tonykoop/chalumeau/build/packet/validation.csv

test_id | variant | target | target_value | measured_value | tolerance | environment | pass_condition | blocking_unknowns | result | action
VAL-001 | all | A4 reference | 440.00 Hz |  | tuner reads 440 within calibration | record temp F, humidity percent | tuner/mic calibration logged before any pitch row | calibrated tuner or reference tone |  | Calibrate tuner/mic before instrument data.
VAL-005 | Soprano C | reed and mouthpiece setup | one reed_id and mouthpiece_id recorded in reed-mouthpiece-capture-template.csv |  | required before pitch claims | same setup ID must appear in prototype/tuning logs | selected setup has reed/mouthpiece identity, gap, onset pressure, response, and leak status | reed model/strength, mouthpiece model/facing, onset pressure, response |  | Do not compare pitch sessions until reed/mouthpiece IDs match.
VAL-008 | Soprano C | bore and trim capture | bore stations plus trim state recorded in bore-trim-capture-template.csv |  | required before final tone-hole tuning | measure before and after bell/foot trim | bore profile and trim history are tied to all-closed measured pitch with the same setup IDs | reed-seat datum, bore station values, measured root pitch |  | Resolve taper/ovalization or datum mismatch before drilling final holes.
VAL-010 | Soprano C | all holes closed | C4, 261.63 Hz |  | +/- 15 cents before final tuning; +/- 8 cents after | 68-72 F preferred | all-closed pitch is logged with reed_id, mouthpiece_id, bore_profile_id, response, and onset pressure | measured_hz, cents_error, response, onset pressure |  | Trim bell end shorter to sharpen; add temporary tape/extension if sharp.
VAL-020 | all | tone-hole sweep | each row in data/tone-hole-schedule.csv |  | +/- 12 cents after tuning | same reed_id, mouthpiece_id, bore_profile_id, and blowing pressure | H01-H07 final rows are within tolerance with response_rating_1_5 >= 3 | final hole diameters, measured_hz, cents_error, response |  | Open hole diameter to sharpen; use wax/tape collar to flatten during tests.
VAL-025 | Soprano C | response sweep | response_rating_1_5 >= 3 and onset_pressure_in_h2o recorded for all closed plus H01-H07 |  | no missing response rows in tuning-capture-template.csv | same reed/mouthpiece setup as tone-hole sweep | every accepted tuning row has onset pressure, response, leak check, and action if response is poor | onset pressure, leak result, response for every note |  | If a note speaks late or chirps, fix leak/reed setup before enlarging holes.
VAL-030 | keyed builds | pad leak test | no visible leak under leak light; suction holds 10 s |  | zero audible hiss at normal blowing pressure | before final tone-hole tuning | K01/K02 pitch rows are accepted only after a leak-light or suction pass | pad seating evidence, suction duration, keyed response |  | Reseat pad, regulate cork, or lap tone-hole rim.
VAL-040 | experimental register key | overblown twelfth check | note + 19 semitones if vent is clarinet-like |  | document response only; not a first-build pass/fail | same reed and embouchure as low-register test | register behavior is logged as research and does not promote first-build readiness | stable low-register response, measured vent response |  | Move/resize vent only after the core chalumeau speaks well.
