tonykoop/chalumeau/validation.csv

gate_id | area | current_status | evidence | pass_condition | blocking_unknowns | next_action | promotion_blocker
VAL-BB-001 | readiness | prototype-validation scaffold | Root packet plus existing build/packet artifacts | All measurement gates below have recorded evidence before L3/build-ready language | measured prototype data, reviewed fabrication authority | Keep README and explorer language at starter/prototype-validation pending | yes
VAL-BB-010 | reed_mouthpiece | measurement_required | build/data/reed-mouthpiece-capture-template.csv | One stable reed_id and mouthpiece_id include make/model, strength, facing or unknown marker, gap, onset pressure, mouthpiece-only response, and leak status | selected reed, mouthpiece, setup, onset pressure, mouthpiece-only pitch/response | Choose commercial reed/mouthpiece and record setup before root tuning | yes
VAL-BB-020 | bore_root_tuning | measurement_required | build/data/bore-trim-capture-template.csv | Reed-seat, mid-bore, and bell-face stations measured; all-closed root logged with same reed_id/mouthpiece_id/bore_profile_id | bore station values, trim history, all-closed measured_hz, cents_error | Measure bore and root before final tone-hole drilling | yes
VAL-BB-030 | tone_holes | measurement_required | build/data/tuning-capture-template.csv plus build/data/tone-hole-schedule.csv | H01-H07 final rows are within +/- 12 cents with response_rating_1_5 >= 3 under the same setup IDs | measured_hz, final hole diameters, cents_error, response | Drill undersized then enlarge in increments and log measured cents error | yes
VAL-BB-040 | keywork | optional_unvalidated | build/hardware/keywork-parts.csv and lever guide | K01/K02 notes are trusted only after leak-light or suction test passes and keyed pitch rows are logged | pad seal, leak-light/suction result, keyed-note response | Run leak-light or suction test before using keyed notes as tuning evidence | yes
VAL-BB-050 | cad_dxf | source_only | build/cad and build/drawings contain starter/source and SVG preview artifacts | Chosen CAD/DXF/design-table authority is reviewed after measured feedback and named in capstone manifest | reviewed authority artifact, measured correction notes | Declare reviewed CAD/DXF/design-table authority before fabrication release | yes
VAL-BB-060 | sourcing | unverified | build/packet/sourcing.csv uses research-needed placeholders | Supplier rows are live-checked at purchase time and marked verified or substitution-candidate | current price, availability, lead time, substitute reed/mouthpiece options | Live-check suppliers plus price plus availability and substitutions before purchase | yes
VAL-BB-070 | photos | missing | Attributed reference photos exist; no Tony-built prototype photos | Public-safe shop photos are captured and attributed separately from reference images | Tony-built prototype images | Capture public-safe build and finished-instrument photos | no
